biohazardxxx/ESP_WiFiSwitch/helperFunctions.ino

//-------------------------------- Help functions ---------------------------


String macToStr(const uint8_t* mac)
{
  String result;
  for (int i = 3; i < 6; ++i) {
    result += String(mac[i], 16);
    if (i < 5)
      result += ':';
  }
  return result;
}


void otaCountown(){
    if(otaCount>0 && otaFlag==1) {
      otaCount--;
      Serial.println(otaCount); 
    }
}
#ifdef WEBOTA
void ota(){
   //Debugln("OTA."); 
   if (OTA.parsePacket()) {
    IPAddress remote = OTA.remoteIP();
    int cmd  = OTA.parseInt();
    int port = OTA.parseInt();
    int size   = OTA.parseInt();

    Serial.print("Update Start: ip:");
    Serial.print(remote);
    Serial.printf(", port:%d, size:%d\n", port, size);
    uint32_t startTime = millis();

    WiFiUDP::stopAll();

    if(!Update.begin(size)){
      Serial.println("Update Begin Error");
      return;
    }

    WiFiClient clientWiFi;
    if (clientWiFi.connect(remote, port)) {

      uint32_t written;
      while(!Update.isFinished()){
        written = Update.write(clientWiFi);
        if(written > 0) clientWiFi.print(written, DEC);
      }
      Serial.setDebugOutput(false);

      if(Update.end()){
        clientWiFi.println("OK");
        Serial.printf("Update Success: %u\nRebooting...\n", millis() - startTime);
        ESP.restart();
      } else {
        Update.printError(clientWiFi);
        Update.printError(Serial);
      }
    } else {
      Serial.printf("Connect Failed: %u\n", millis() - startTime);
    }
  }
  //IDE Monitor (connected to Serial)
  if (TelnetServer.hasClient()){
    if (!Telnet || !Telnet.connected()){
      if(Telnet) Telnet.stop();
      Telnet = TelnetServer.available();
    } else {
      WiFiClient toKill = TelnetServer.available();
      toKill.stop();
    }
  }
  if (Telnet && Telnet.connected() && Telnet.available()){
    while(Telnet.available())
      Serial.write(Telnet.read());
  }
  if(Serial.available()){
    size_t len = Serial.available();
    uint8_t * sbuf = (uint8_t *)malloc(len);
    Serial.readBytes(sbuf, len);
    if (Telnet && Telnet.connected()){
      Telnet.write((uint8_t *)sbuf, len);
      yield();
    }
    free(sbuf);
  }
}
#endif
